CameronHope1/hw_numpad/wiring_schematic/hw_numpad_diagram.kicad_sch

## KiCad design wiring_schematic/hw_numpad_diagram.kicad_sch (2026-07-03)

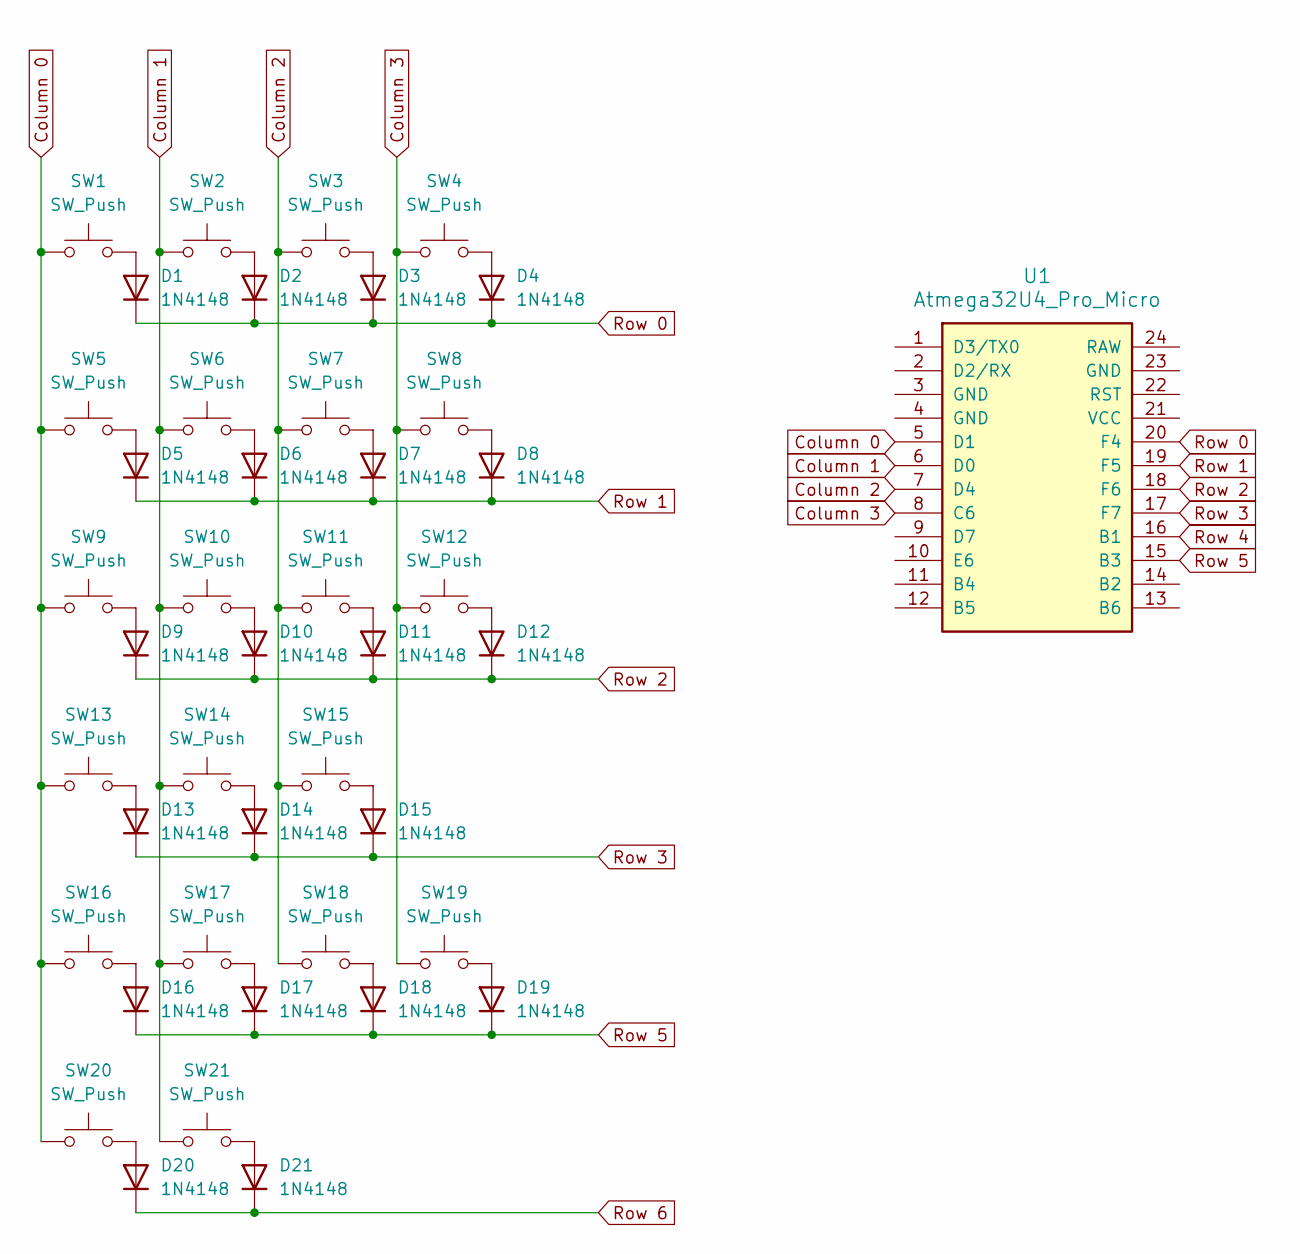
[picture p3: schematic hw_numpad_diagram.kicad_sch]

Parts:
D1, D2, D3, D4, D5, D6, D7, D8, D9, D10, D11, D12, D13, D14, D15, D16, D17, D18, D19, D20, D21: 1N4148; D_DO-35_SOD27_P7.62mm_Horizontal
SW1, SW2, SW3, SW4, SW5, SW6, SW7, SW8, SW9, SW10, SW11, SW12, SW13, SW14, SW15, SW16, SW17, SW18, SW19, SW20, SW21: SW_Push
U1: Atmega32U4_Pro_Micro; Sparkfun_Pro_Micro

Connections:
Column 0: SW1.1, SW5.1, SW9.1, SW13.1, SW16.1, SW20.1, U1.5 (D1)
Column 1: SW2.1, SW6.1, SW10.1, SW14.1, SW17.1, SW21.1, U1.6 (D0)
Column 2: SW3.1, SW7.1, SW11.1, SW15.1, SW18.1, U1.7 (D4)
Column 3: SW4.1, SW8.1, SW12.1, SW19.1, U1.8 (C6)
unnamed: D1.2 (A), SW1.2
unnamed: D2.2 (A), SW2.2
unnamed: D3.2 (A), SW3.2
unnamed: D4.2 (A), SW4.2
unnamed: D5.2 (A), SW5.2
unnamed: D6.2 (A), SW6.2
unnamed: D7.2 (A), SW7.2
unnamed: D8.2 (A), SW8.2
unnamed: D9.2 (A), SW9.2
unnamed: D10.2 (A), SW10.2
unnamed: D11.2 (A), SW11.2
unnamed: D12.2 (A), SW12.2
unnamed: D13.2 (A), SW13.2
unnamed: D14.2 (A), SW14.2
unnamed: D15.2 (A), SW15.2
unnamed: D16.2 (A), SW16.2
unnamed: D17.2 (A), SW17.2
unnamed: D18.2 (A), SW18.2
unnamed: D19.2 (A), SW19.2
unnamed: D20.2 (A), SW20.2
unnamed: D21.2 (A), SW21.2
Row 0: D1.1 (K), D2.1 (K), D3.1 (K), D4.1 (K), U1.20 (F4)
Row 1: D5.1 (K), D6.1 (K), D7.1 (K), D8.1 (K), U1.19 (F5)
Row 2: D9.1 (K), D10.1 (K), D11.1 (K), D12.1 (K), U1.18 (F6)
Row 3: D13.1 (K), D14.1 (K), D15.1 (K), U1.17 (F7)
Row 4: U1.16 (B1)
Row 5: D16.1 (K), D17.1 (K), D18.1 (K), D19.1 (K), U1.15 (B3)
Row 6: D20.1 (K), D21.1 (K)
